thingSoC/TSOC_GROVEY_GPIO/TSOC_GROVEY_GPIO/eagleUp/eagleUp_TSOC_GROVEY_GPIO_board_top.jpg

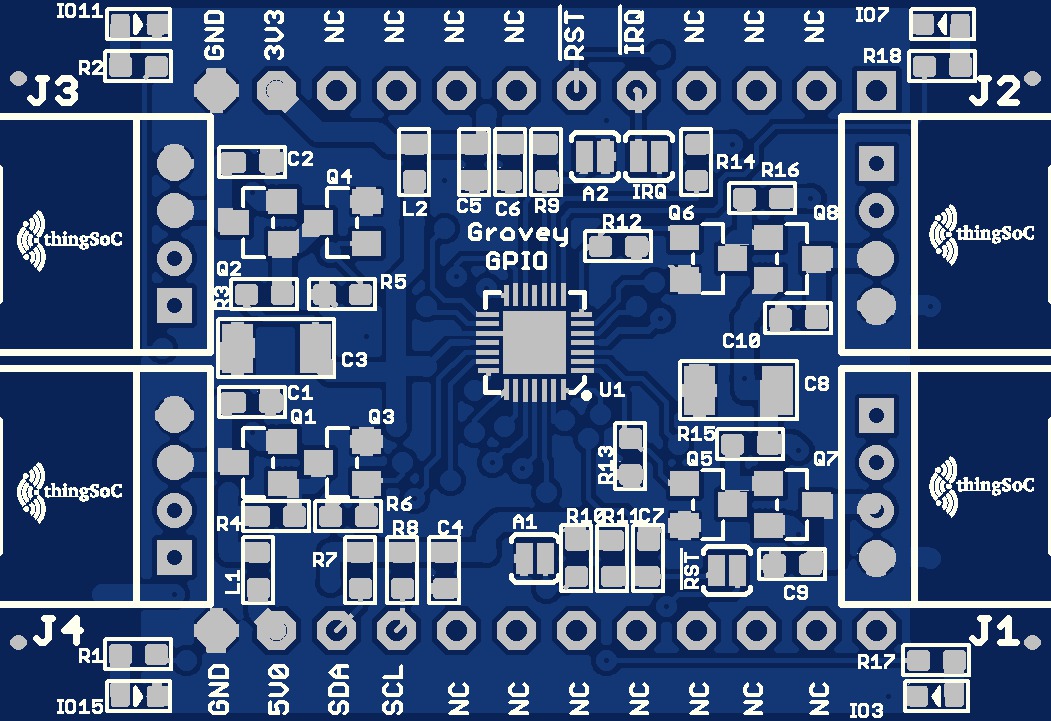
TSOC_GROVEY_GPIO/eagleUp/eagleUp_TSOC_GROVEY_GPIO_board_top.jpg
