thingSoC/TSOC_GROVEY_GPIO/TSOC_GROVEY_GPIO/images/raw/TSOC_GROVEY_GPIO_bot_raw.png

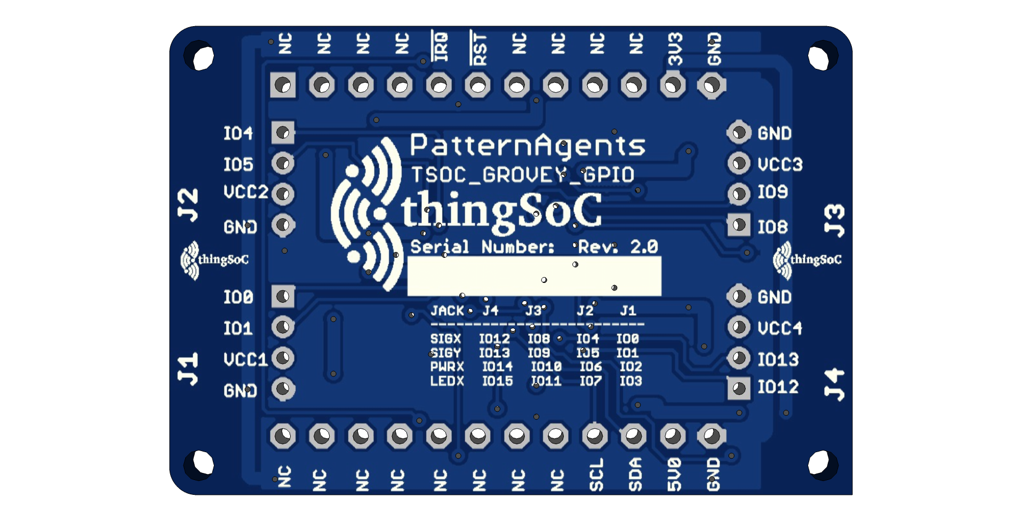
TSOC_GROVEY_GPIO/images/raw/TSOC_GROVEY_GPIO_bot_raw.png
