thingSoC/TSOC_GROVEY_GPIO/TSOC_GROVEY_GPIO/images/raw/TSOC_GROVEY_GPIO_iso_raw.png

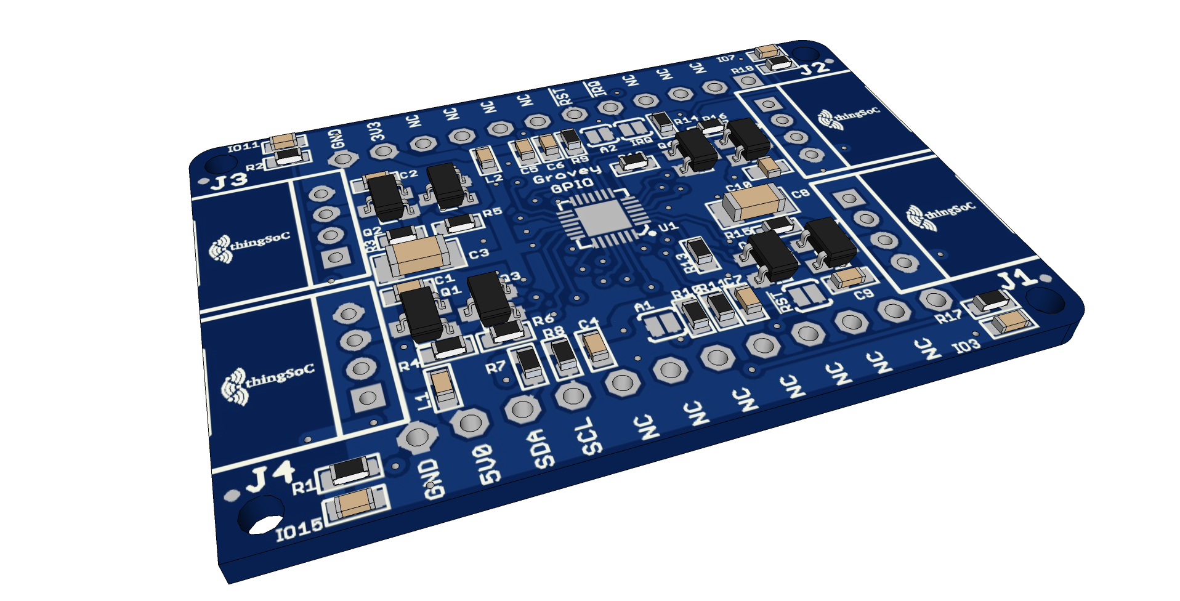
TSOC_GROVEY_GPIO/images/raw/TSOC_GROVEY_GPIO_iso_raw.png
