thingSoC/TSOC_GROVEY_GPIO/TSOC_GROVEY_GPIO/images/TSOC_GROVEY_GPIO_iso.png

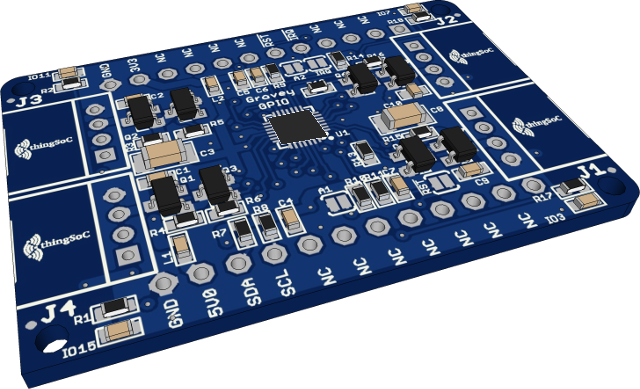
TSOC_GROVEY_GPIO/images/TSOC_GROVEY_GPIO_iso.png
